Jezen5Volk/Transparent-MEA/64 Electrode Stimulation/Stimulation_Board/DAC_Commands.h

#ifndef DAC_COMMANDS
#define DAC_COMMANDS

#define N_DACS 4 //There are 4 DACs on the Stimulation Board
#define DAC_RES (5.0/4095) //Max voltage is 5, 12 bit DAC, so resolution is 5/(2^12-1)

#define RESETpin 10
#define SYNCpin 14
#define LDACpin 15

#include <string>
#include <vector> 

class DAC
{
    public:
    
    /*-----------------
    Low Level Functions
    -----------------*/
    void xfer_data(std::string data, int size);
    void reset(); //Resets to zero scale

    /*--------------------
    Medium Level Functions
    --------------------*/
    void DCEN(); //Daisy Chain Enable  
    void write_DAC_reg(float voltage, int reg); //Write a voltage to a DAC Register

    /*------------------
    High Level Functions
    ------------------*/
    void ref_reset(); //Resets all DAC outputs to REF voltage (2.5 V) 
    void sync_write(float voltage, std::vector<int> regs); //Writes voltage to selected registers simultaneously
    void seq_write(float voltage, std::vector<int> regs, long unsigned int delay_msec); //Writes voltage to selected registers sequentially with delay in mSec
    void p_pulse(unsigned long int e_dly, unsigned long int puls_dur_pos, unsigned long int puls_dur_neg, unsigned long int brst_dur, float amp_pos, float amp_neg, std::vector<int> regs); 

};



#endif 
